WB2CBA/DX-FT8-FT8-MULTIBAND-TABLET-TRANSCEIVER/DX FT8 3D CASE FILES/DXFT8_-_Case_Bottom_12mm_Bottom_Layer_Spacers.png

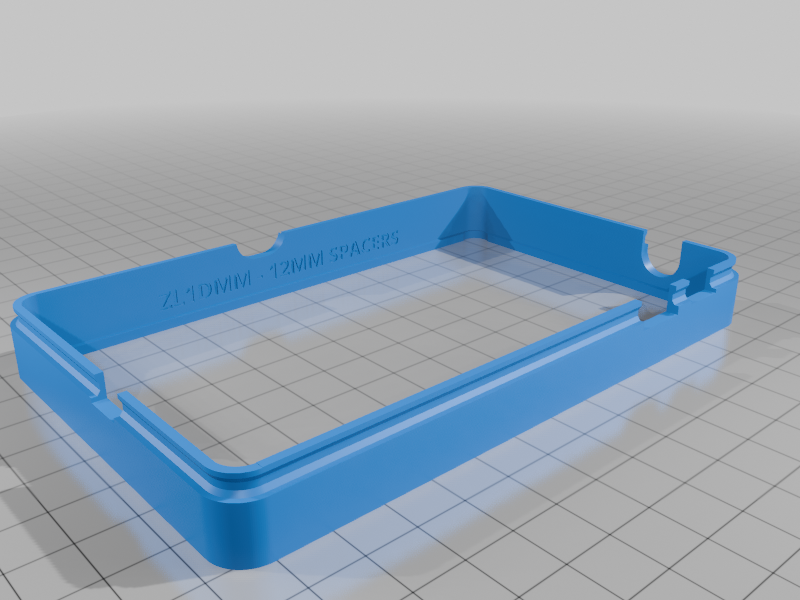
DX FT8 3D CASE FILES/DXFT8_-_Case_Bottom_12mm_Bottom_Layer_Spacers.png
