WB2CBA/DX-FT8-FT8-MULTIBAND-TABLET-TRANSCEIVER/DX FT8 3D CASE FILES/DXFT8_-_Case_Door.png

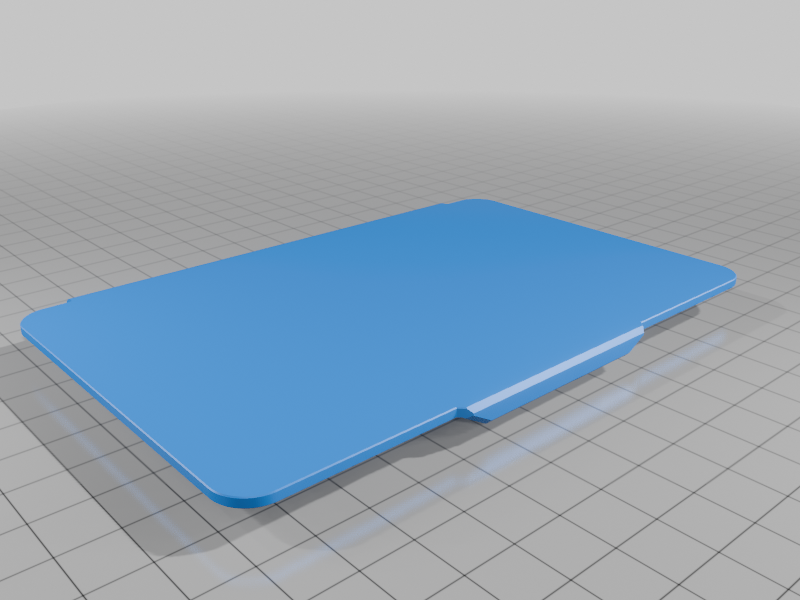
DX FT8 3D CASE FILES/DXFT8_-_Case_Door.png
