WB2CBA/DX-FT8-FT8-MULTIBAND-TABLET-TRANSCEIVER/DX FT8 5 BAND RF PCB INFOMATON/DX FT8 RF BOARD.jpg

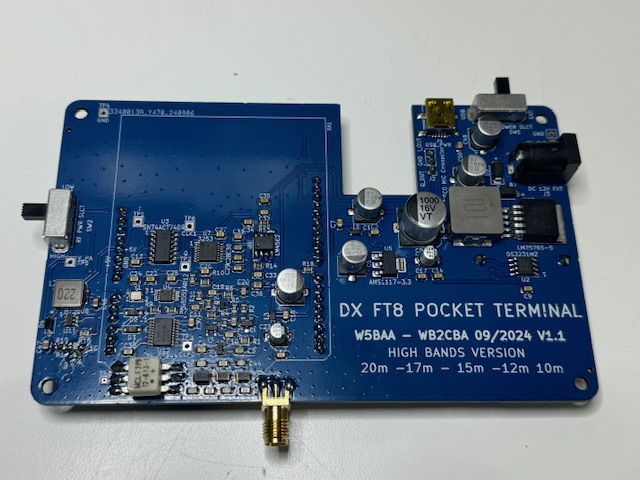
DX FT8 5 BAND RF PCB INFOMATON/DX FT8 RF BOARD.jpg
