WB2CBA/DX-FT8-FT8-MULTIBAND-TABLET-TRANSCEIVER/DX FT8 7 BAND PCB INFORMATION/DX FT8 7 BANDS V2 DFM ANALYSIS.png

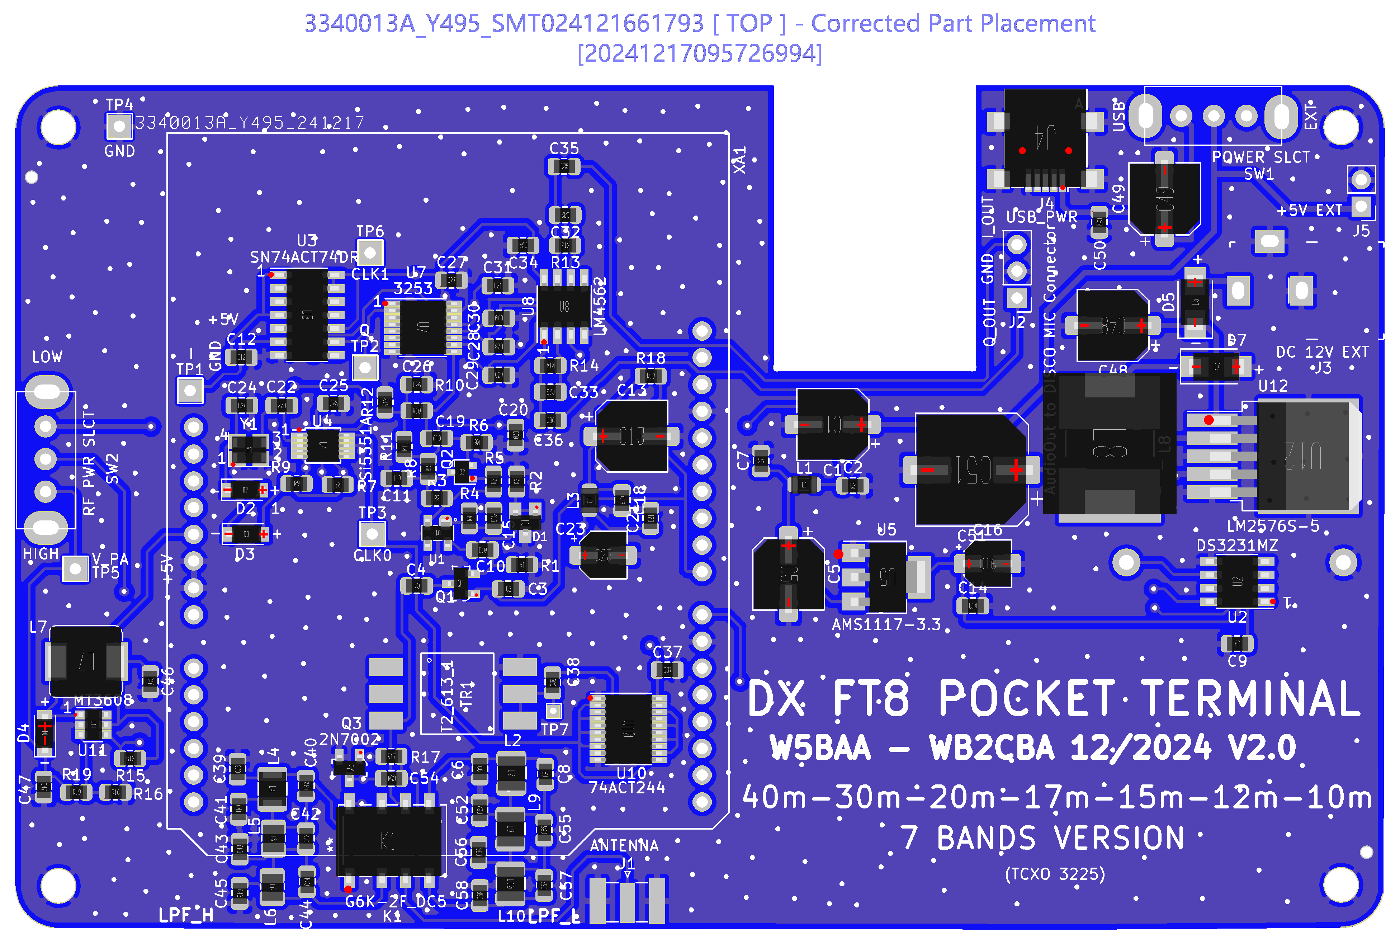
DX FT8 7 BAND PCB INFORMATION/DX FT8 7 BANDS V2 DFM ANALYSIS.png
