WB2CBA/DX-FT8-FT8-MULTIBAND-TABLET-TRANSCEIVER/DX FT8 7 BAND PCB INFORMATION/DX FT8 V2 7 Band PCB.jpg

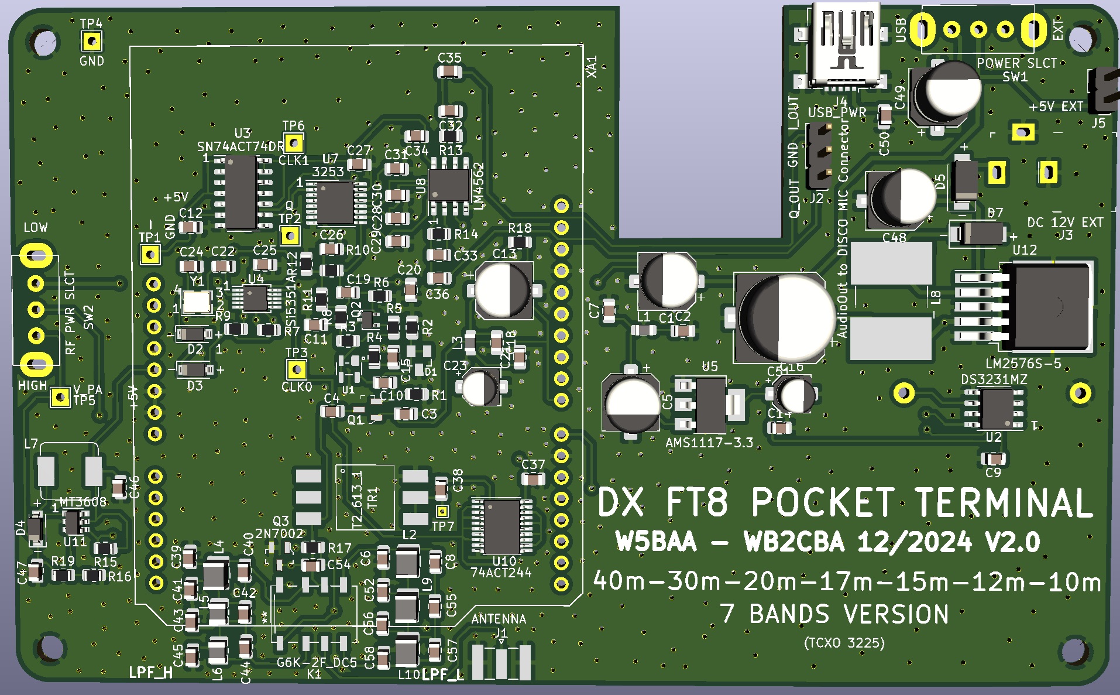
DX FT8 7 BAND PCB INFORMATION/DX FT8 V2 7 Band PCB.jpg
