WB2CBA/DX-FT8-FT8-MULTIBAND-TABLET-TRANSCEIVER/IMG_1915.jpg

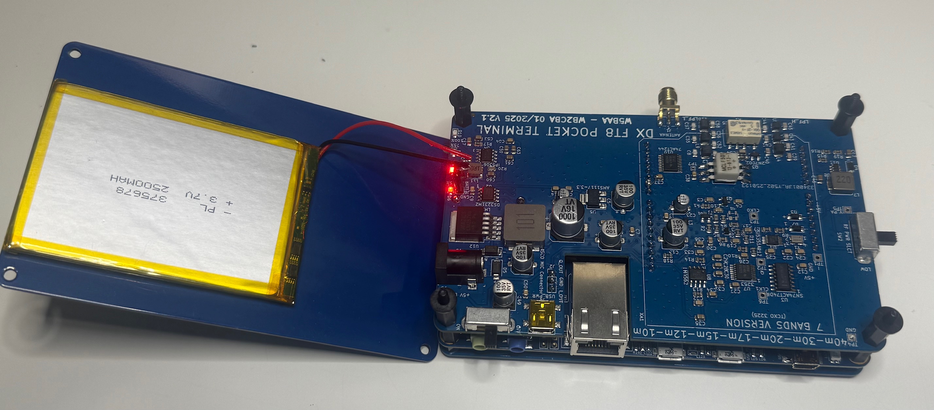
IMG_1915.jpg
