WB2CBA/DX-FT8-FT8-MULTIBAND-TABLET-TRANSCEIVER/IMG_1917.jpg

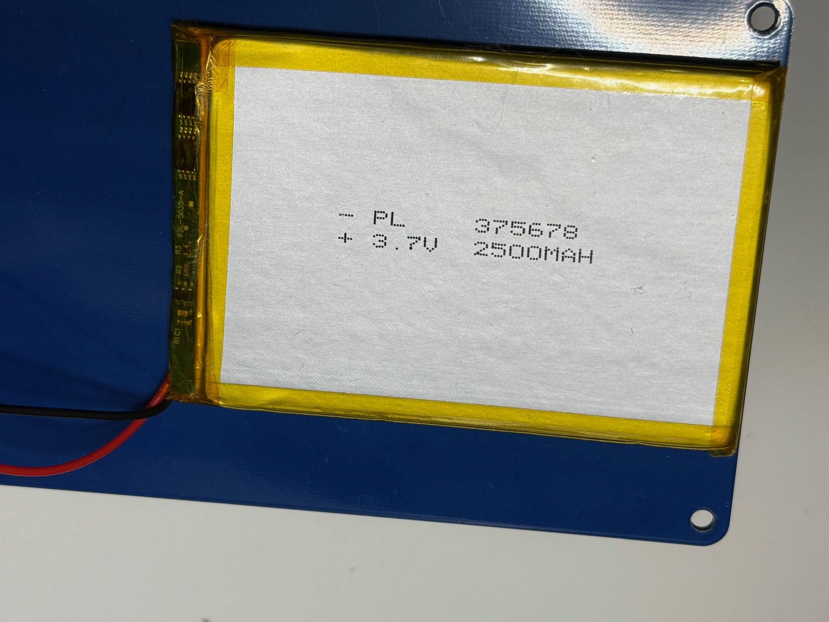
IMG_1917.jpg
