WB2CBA/DX-FT8-FT8-MULTIBAND-TABLET-TRANSCEIVER/DX FT8 7 BAND PCB INFORMATION/DX FT8 SOLDER SIDE LAYOUT.jpg

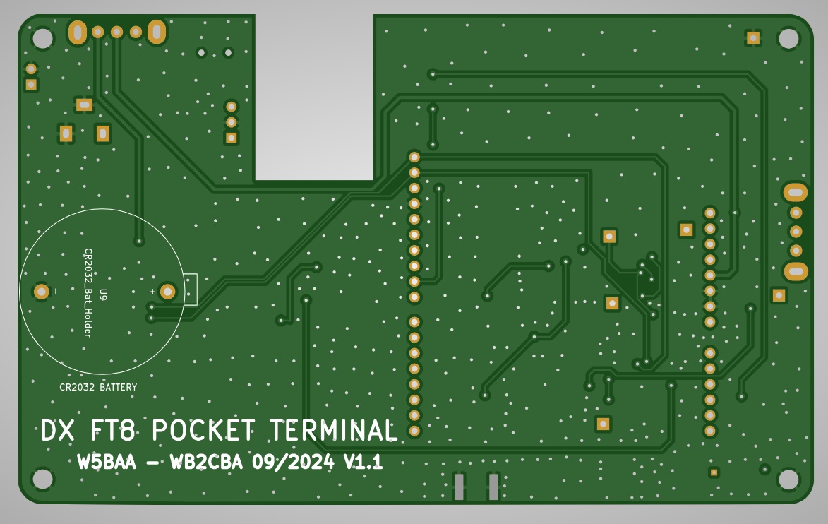
DX FT8 7 BAND PCB INFORMATION/DX FT8 SOLDER SIDE LAYOUT.jpg
