WB2CBA/DX-FT8-FT8-MULTIBAND-TABLET-TRANSCEIVER/DX FT8 FIRMWARE/Check this for how to Download Firmware.jpg

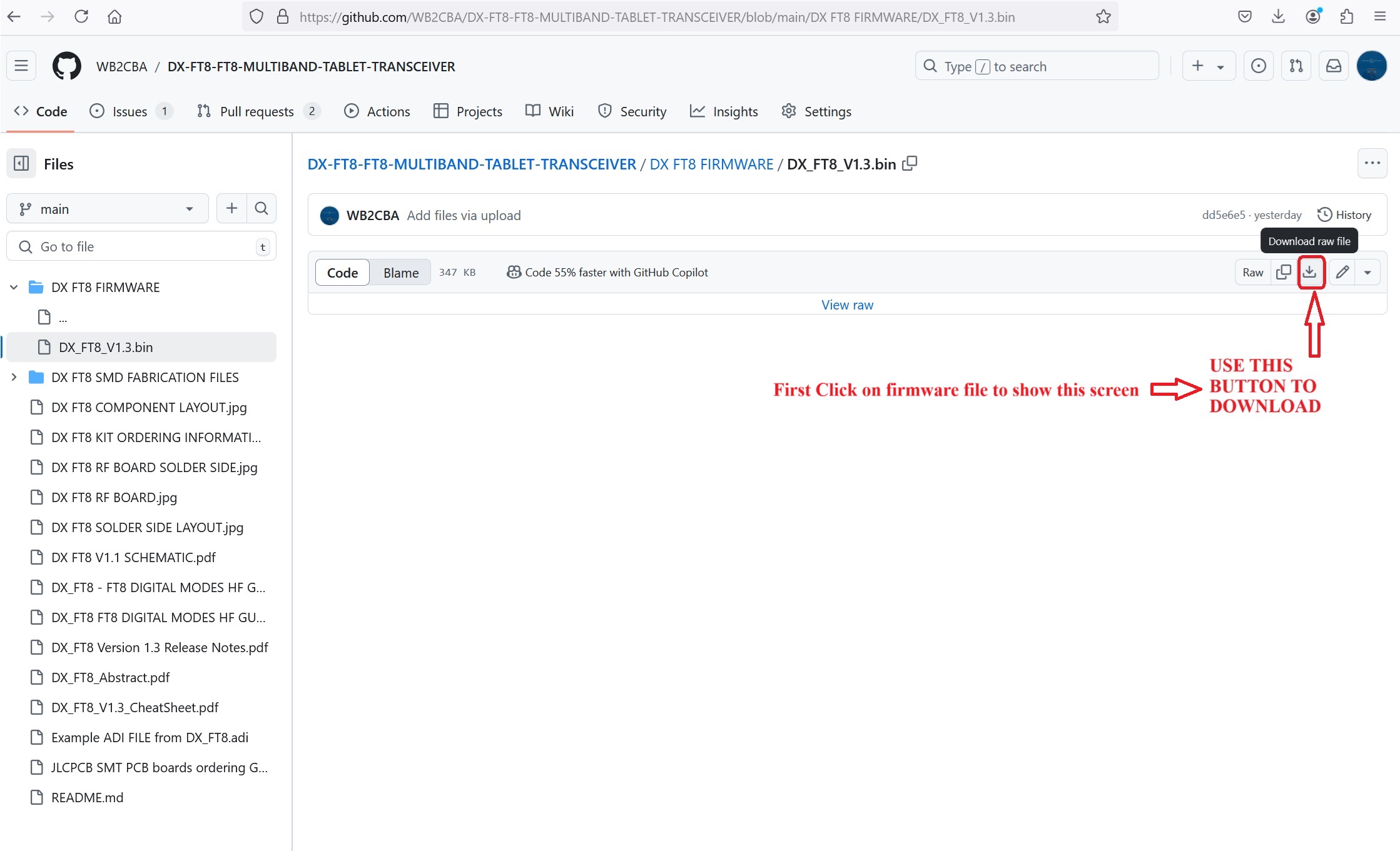
DX FT8 FIRMWARE/Check this for how to Download Firmware.jpg
